mcrouper/maratui-waage/src/state/fsm.rs

use log::{error, info};

use super::global_state::MACHINE_OFFLINE_TIMEOUT;
use super::{
    AppError, AppEvent, CalibrationStep, ConnectionStatus, DeviceInfo, ExtractionState,
    GlobalAppState,
};
use crate::button::{Button, ButtonPressType};
#[cfg(feature = "home-assistant")]
use crate::home_assistant;
use crate::screens::Screen;
use crate::telemetry::{TelemetryFrame, update_state_with_events};
use std::time::{Duration, Instant};

/// Application state machine
/// Handles events and updates the global application state
pub struct AppStateMachine;

impl AppStateMachine {
    /// Handle an application event and update the state
    pub fn handle_event(state: &mut GlobalAppState, event: AppEvent) {
        info!("Handling event: {:?}", event);

        if event.is_telemetry_event() {
            state.events_log.push_front(format!("Event: {:?}", event));
            if state.events_log.len() > 10 {
                state.events_log.pop_back();
            }
        }
        match event {
            // ===== Telemetry Events =====
            AppEvent::ShotStarted => {
                state.extraction_state = ExtractionState::Extracting {
                    started_at: Instant::now(),
                };
                state.error = None;
                // Tare out whatever is currently on the scale (e.g. the empty cup) so the
                // Dashboard shows net extracted weight for this shot.
                Self::tare_scale(state);
            }

            AppEvent::ShotEnded { duration } => {
                state.extraction_state = ExtractionState::Idle {
                    last_extraction_duration: Some(Duration::from_secs(duration)),
                };
                state.last_shot_ended_at = Some(Instant::now());
            }

            AppEvent::ShotAborted { .. } => {
                state.extraction_state = ExtractionState::Idle {
                    last_extraction_duration: None,
                };
                state.last_shot_ended_at = Some(Instant::now());
            }

            AppEvent::ModeChanged { from: _, to: _ } => {
                // Machine mode is already updated in MachineState
                // Additional logic can be added here if needed
            }

            AppEvent::WaterRefillNeeded { code } => {
                state.error = Some(AppError::WaterRefillNeeded { code });
            }

            AppEvent::WaterRefillCleared => {
                state.error = None;
            }

            // ===== UI Events =====
            AppEvent::NextScreen => {
                state.current_screen = state.current_screen.next();
            }

            AppEvent::PreviousScreen => {
                state.current_screen = state.current_screen.previous();
            }

            AppEvent::DebugScreen => {
                if state.current_screen == Screen::Debug {
                    state.current_screen = state
                        .screen_before_debug
                        .take()
                        .unwrap_or(Screen::Dashboard);
                } else {
                    state.screen_before_debug = Some(state.current_screen);
                    state.current_screen = Screen::Debug;
                }
                // Debug uses a full-screen layout unrelated to the normal screens; clear so
                // nothing from the previous layout lingers.
                state.request_redraw();
            }

            AppEvent::ErrorOccurred { error } => {
                state.error = Some(AppError::MachineOffline);
                // Log the error (logging can be added here)
                error!("Application error: {}", error);
            }

            AppEvent::ErrorCleared => {
                state.error = None;
            }

            AppEvent::WifiStatusChanged(status) => {
                match &status {
                    ConnectionStatus::Connected | ConnectionStatus::Disconnected => {
                        state.events_log.push_front(format!("Wi-Fi: {:?}", status));
                        if state.events_log.len() > 10 {
                            state.events_log.pop_back();
                        }
                    }
                    _ => {}
                }
                state.wifi_status = status;
            }

            AppEvent::MqttStatusChanged(status) => {
                let should_log = match &status {
                    ConnectionStatus::Connected => state.mqtt_status != ConnectionStatus::Connected,
                    ConnectionStatus::Disconnected | ConnectionStatus::Error(_) => true,
                    _ => false,
                };
                if should_log {
                    state.events_log.push_front(format!("MQTT: {:?}", status));
                    if state.events_log.len() > 10 {
                        state.events_log.pop_back();
                    }
                }
                state.mqtt_status = status;
            }

            AppEvent::CupCounterUpdated { cups } => {
                state.cup_counter = Some(cups);
            }

            AppEvent::PublishMqttEvent {
                topic_suffix,
                payload,
            } => {
                state.enqueue_mqtt_message(topic_suffix, payload);
            }

            AppEvent::DeviceInfoUpdated(info) => {
                let payload = device_status_payload(&info);
                #[cfg(feature = "home-assistant")]
                home_assistant::enqueue_status_states(state, &info);
                state.device_info = info;
                state.enqueue_mqtt_message("status", payload);
            }

            AppEvent::LoadingStage { message, progress } => {
                state.loading_status = Some((message, progress));
            }

            AppEvent::LoadingComplete => {
                state.loading_status = Some(("waiting for machine...", 100));
            }

            AppEvent::EnterOfflineMode => {
                if state.machine_state.last_frame.is_none() {
                    state.machine_state.last_frame = Some(TelemetryFrame::offline_frame());
                    state.offline_mode = true;
                    state.last_activity_at = Some(Instant::now());
                    state.request_redraw();
                }
            }

            AppEvent::WeightUpdated { weight_dg } => {
                if state.last_raw_weight_dg.is_none() {
                    // First reading since boot: tare immediately so the Dashboard starts at
                    // 0g instead of showing whatever residual raw drift happens to be on the
                    // scale (e.g. the portafilter, or just calibration offset error).
                    state.scale_tare_dg = weight_dg;
                }
                state.last_raw_weight_dg = Some(weight_dg);
                state.weight_dg = Some(weight_dg - state.scale_tare_dg);
                Self::publish_weight_if_due(state, Instant::now());
            }

            AppEvent::RawWeightUpdated { left, right } => {
                state.raw_weight_left = left;
                state.raw_weight_right = right;
            }

            AppEvent::StartCalibration => {
                if state.calibration_step.is_none() {
                    state.screen_before_calibration = Some(state.current_screen);
                    state.calibration_step = Some(CalibrationStep::ConfirmEmptyLeft);
                    state.request_redraw();
                }
            }

            AppEvent::CalibrationConfirm => {
                state.calibration_step = match state.calibration_step {
                    Some(CalibrationStep::ConfirmEmptyLeft) => Some(CalibrationStep::TaringLeft),
                    Some(CalibrationStep::ConfirmReferenceLeft) => {
                        Some(CalibrationStep::CalibratingLeft)
                    }
                    Some(CalibrationStep::ConfirmEmptyRight) => Some(CalibrationStep::TaringRight),
                    Some(CalibrationStep::ConfirmReferenceRight) => {
                        Some(CalibrationStep::CalibratingRight)
                    }
                    // A press on the result screen dismisses the wizard.
                    Some(CalibrationStep::Done { .. }) => None,
                    other => other,
                };
                if state.calibration_step.is_none() {
                    if let Some(prev) = state.screen_before_calibration.take() {
                        state.current_screen = prev;
                    }
                    state.request_redraw();
                }
            }

            AppEvent::CalibrationCancel => {
                state.calibration_step = None;
                if let Some(prev) = state.screen_before_calibration.take() {
                    state.current_screen = prev;
                }
                state.request_redraw();
            }

            AppEvent::CalibrationStepResult { success } => {
                state.calibration_step = Some(match (state.calibration_step, success) {
                    (Some(CalibrationStep::TaringLeft), true) => {
                        CalibrationStep::ConfirmReferenceLeft
                    }
                    (Some(CalibrationStep::CalibratingLeft), true) => {
                        CalibrationStep::ConfirmEmptyRight
                    }
                    (Some(CalibrationStep::TaringRight), true) => {
                        CalibrationStep::ConfirmReferenceRight
                    }
                    (Some(CalibrationStep::CalibratingRight), true) => {
                        CalibrationStep::Done { success: true }
                    }
                    _ => CalibrationStep::Done { success: false },
                });
            }
        }
    }

    /// Handle button press events
    pub fn handle_button_press(state: &mut GlobalAppState, button: Button) {
        // While the calibration wizard is active, button presses drive it instead of the
        // usual screen navigation / Debug toggle.
        if state.calibration_step.is_some() {
            match button {
                Button::Button1(ButtonPressType::Short) => {
                    Self::handle_event(state, AppEvent::CalibrationConfirm);
                }
                Button::Button1(ButtonPressType::Long) => {
                    Self::handle_event(state, AppEvent::CalibrationCancel);
                }
                // Double press has no meaning inside the wizard; ignore it.
                Button::Button1(ButtonPressType::Double) => {}
            }
            return;
        }

        // Long press always toggles Debug, even during loading.
        if let Button::Button1(ButtonPressType::Long) = button {
            Self::handle_event(state, AppEvent::DebugScreen);
            return;
        }

        // Double press manually zeros the scale, regardless of screen — a quick way to tare
        // without waiting for a shot to start.
        if let Button::Button1(ButtonPressType::Double) = button {
            Self::tare_scale(state);
            return;
        }

        // During loading: short press manually toggles the backlight.
        if state.machine_state.last_frame.is_none() {
            if let Button::Button1(ButtonPressType::Short) = button {
                state.backlight_on = !state.backlight_on;
            }
            return;
        }

        // Normal operation after first UART frame arrives.
        let now = Instant::now();
        let backlight_was_on = state.backlight_should_be_on(now);
        state.last_activity_at = Some(now);

        // If the screen was dark (backlight timed out), the first press only wakes the
        // backlight and must not also switch screens.
        if !backlight_was_on {
            return;
        }

        if let Button::Button1(ButtonPressType::Short) = button
            && state.current_screen != Screen::Debug
        {
            Self::handle_event(state, AppEvent::NextScreen);
        }
    }

    /// Zero the scale: tare both cells against whatever they're currently reading, so the
    /// Dashboard's weight display resets to 0 g. Shared by the shot-start auto-tare and the
    /// manual double-press-to-zero gesture.
    fn tare_scale(state: &mut GlobalAppState) {
        state.scale_tare_dg = state.last_raw_weight_dg.unwrap_or(0);
        state.weight_dg = Some(0);
    }

    /// Publish the displayed (tared) weight to `<prefix>/scale` when it changed, at most once per
    /// `SCALE_PUBLISH_INTERVAL`. A change that falls inside the interval isn't lost: the scale
    /// keeps sampling, so the next `WeightUpdated` after the interval publishes the latest value.
    fn publish_weight_if_due(state: &mut GlobalAppState, now: Instant) {
        let Some(weight_dg) = state.weight_dg else {
            return;
        };
        if state.last_published_weight_dg == Some(weight_dg) {
            return;
        }
        let due = state
            .last_scale_publish_at
            .map(|t| now.saturating_duration_since(t) >= SCALE_PUBLISH_INTERVAL)
            .unwrap_or(true);
        if !due {
            return;
        }
        state.last_published_weight_dg = Some(weight_dg);
        state.last_scale_publish_at = Some(now);
        state.enqueue_mqtt_message("scale", scale_payload(weight_dg));
    }

    /// Handle telemetry frame updates
    pub fn handle_telemetry_frame(state: &mut GlobalAppState, frame: TelemetryFrame, now: Instant) {
        state.offline_mode = false;
        state.enqueue_mqtt_message("telemetry", telemetry_payload(&frame));

        // A new session starts on the very first frame, or when telemetry resumes after the
        // machine has been offline (long UART gap). Reset per-session state and ask the render
        // loop to clear the terminal so any accumulated display artifacts are wiped.
        let new_session = state
            .last_uart_frame_at
            .map(|t| now.saturating_duration_since(t) >= MACHINE_OFFLINE_TIMEOUT)
            .unwrap_or(true);
        if new_session {
            state.machine_state.reset_session();
            state.request_redraw();
        }

        // frame moves into update_state_with_events; it is stored in state.machine_state.last_frame
        let (_snapshot, events) = update_state_with_events(&mut state.machine_state, frame, now);

        // Extract Copy fields from last_frame before the mutable borrows below
        let (boiler_target, boiler_now_c, hx_now_c) = {
            let last = state
                .machine_state
                .last_frame
                .as_ref()
                .expect("update_state_with_events always stores the frame in last_frame");
            (
                last.boiler_target_c.map(f64::from).unwrap_or_default(),
                f64::from(last.boiler_now_c),
                f64::from(last.hx_now_c),
            )
        };
        let should_sample = state
            .machine_state
            .last_graph_sample_at
            .map(|t| now.saturating_duration_since(t) >= GRAPH_SAMPLE_INTERVAL)
            .unwrap_or(true);
        if should_sample {
            state.machine_state.last_graph_sample_at = Some(now);
            push_sample(&mut state.machine_state.target_boiler_data, boiler_target);
            push_sample(&mut state.machine_state.current_boiler_data, boiler_now_c);
            push_sample(&mut state.machine_state.current_hx_data, hx_now_c);
            state.machine_state.rebuild_graph_points();
        }
        state.last_activity_at = Some(now);
        state.last_uart_frame_at = Some(now);

        // Process each event through the FSM
        for event in events {
            let event_payload = telemetry_event_payload(&event, state.weight_dg);
            #[cfg(feature = "home-assistant")]
            home_assistant::enqueue_event_states(state, &event);
            Self::handle_event(state, AppEvent::from_telemetry(event));
            state.enqueue_mqtt_message("events", event_payload);
        }

        #[cfg(feature = "home-assistant")]
        home_assistant::enqueue_telemetry_states(state);
    }

    /// Handle multiple events in sequence
    pub fn handle_events(state: &mut GlobalAppState, events: Vec<AppEvent>) {
        for event in events {
            Self::handle_event(state, event);
        }
    }
}

fn json_opt_num<T: std::fmt::Display>(opt: Option<T>) -> String {
    opt.map_or_else(|| "null".to_string(), |v| v.to_string())
}

fn json_opt_str(opt: Option<&str>) -> String {
    opt.map_or_else(|| "null".to_string(), |s| format!("\"{}\"", s))
}

fn telemetry_payload(frame: &TelemetryFrame) -> String {
    format!(
        "{{\"mode\":\"{}\",\"sw\":\"{}\",\"boiler_now_c\":{},\"boiler_target_c\":{},\"hx_now_c\":{},\"boost_countdown_s\":{},\"heating_on\":{},\"pump_on\":{},\"no_water_code\":{}}}",
        frame.mode,
        frame.sw_version,
        frame.boiler_now_c,
        json_opt_num(frame.boiler_target_c),
        frame.hx_now_c,
        frame.boost_countdown_s,
        frame.heating_on,
        frame.pump_on,
        json_opt_num(frame.no_water_code),
    )
}

/// One sample per second; 300 samples = 5-minute window shown on the Graphs screen.
const GRAPH_BUF_CAP: usize = 300;
const GRAPH_SAMPLE_INTERVAL: Duration = Duration::from_secs(1);

fn push_sample(buf: &mut std::collections::VecDeque<f64>, value: f64) {
    buf.push_back(value);
    if buf.len() > GRAPH_BUF_CAP {
        buf.pop_front();
    }
}

/// Cap on `<prefix>/scale` publishes (~4 Hz), so sub-gram noise can't flood the MQTT queue.
const SCALE_PUBLISH_INTERVAL: Duration = Duration::from_millis(250);

/// Format decigrams as grams with one decimal (`-5` → `-0.5`), exact — no float rounding.
fn grams_json(weight_dg: i32) -> String {
    let sign = if weight_dg < 0 { "-" } else { "" };
    let abs = weight_dg.unsigned_abs();
    format!("{}{}.{}", sign, abs / 10, abs % 10)
}

fn opt_grams_json(weight_dg: Option<i32>) -> String {
    weight_dg.map_or_else(|| "null".to_string(), grams_json)
}

fn scale_payload(weight_dg: i32) -> String {
    format!("{{\"weight_g\":{}}}", grams_json(weight_dg))
}

fn device_status_payload(info: &DeviceInfo) -> String {
    format!(
        "{{\"uptime_s\":{},\"wifi_ssid\":\"{}\",\"wifi_rssi\":{},\"ip\":{},\"free_heap_b\":{},\"last_telemetry_age_s\":{}}}",
        info.uptime_s,
        info.wifi_ssid,
        json_opt_num(info.wifi_rssi),
        json_opt_str(info.ip.as_deref()),
        json_opt_num(info.free_heap_b),
        json_opt_num(info.last_telemetry_age_s),
    )
}

/// `weight_dg` is the net (shot-start-tared) scale weight at the moment the event fires, so for
/// `shot_ended`/`shot_aborted` it's the shot's yield; `null` without a scale.
fn telemetry_event_payload(event: &crate::telemetry::AppEvent, weight_dg: Option<i32>) -> String {
    match event {
        crate::telemetry::AppEvent::ShotStarted => "{\"type\":\"shot_started\"}".to_string(),
        crate::telemetry::AppEvent::ShotEnded { duration } => format!(
            "{{\"type\":\"shot_ended\",\"duration\":{},\"weight_g\":{}}}",
            duration,
            opt_grams_json(weight_dg)
        ),
        crate::telemetry::AppEvent::ShotAborted { duration } => format!(
            "{{\"type\":\"shot_aborted\",\"duration\":{},\"weight_g\":{}}}",
            duration,
            opt_grams_json(weight_dg)
        ),
        crate::telemetry::AppEvent::WaterRefillNeeded { code } => {
            format!("{{\"type\":\"water_refill_needed\",\"code\":{}}}", code)
        }
        crate::telemetry::AppEvent::WaterRefillCleared => {
            "{\"type\":\"water_refill_cleared\"}".to_string()
        }
        crate::telemetry::AppEvent::ModeChanged { from, to } => {
            format!(
                "{{\"type\":\"mode_changed\",\"from\":\"{}\",\"to\":\"{}\"}}",
                from, to
            )
        }
    }
}

#[cfg(test)]
mod tests {
    use super::*;
    use crate::screens::Screen;
    use crate::state::global_state::BACKLIGHT_TIMEOUT;
    use std::time::Duration;

    #[test]
    fn test_handle_shot_started() {
        let mut state = GlobalAppState::default();
        assert_eq!(
            state.extraction_state,
            ExtractionState::Idle {
                last_extraction_duration: None
            }
        );

        AppStateMachine::handle_event(&mut state, AppEvent::ShotStarted);

        assert!(state.extraction_state.is_extracting());
    }

    #[test]
    fn test_handle_shot_ended() {
        let mut state = GlobalAppState::default();
        state.extraction_state = ExtractionState::Extracting {
            started_at: Instant::now(),
        };

        let duration = Duration::from_secs(30);
        AppStateMachine::handle_event(
            &mut state,
            AppEvent::ShotEnded {
                duration: duration.as_secs(),
            },
        );

        assert_eq!(
            state.extraction_state,
            ExtractionState::Idle {
                last_extraction_duration: Some(duration)
            }
        );
    }

    #[test]
    fn test_handle_water_refill_needed() {
        let mut state = GlobalAppState::default();
        assert!(!state.has_error());

        AppStateMachine::handle_event(&mut state, AppEvent::WaterRefillNeeded { code: 65 });

        assert!(state.has_error());
        assert_eq!(state.error, Some(AppError::WaterRefillNeeded { code: 65 }));
    }

    #[test]
    fn test_handle_water_refill_cleared() {
        let mut state = GlobalAppState::default();
        state.error = Some(AppError::WaterRefillNeeded { code: 65 });

        AppStateMachine::handle_event(&mut state, AppEvent::WaterRefillCleared);

        assert!(!state.has_error());
    }

    #[test]
    fn test_handle_next_screen() {
        let mut state = GlobalAppState::default();
        let initial_screen = state.current_screen;

        AppStateMachine::handle_event(&mut state, AppEvent::NextScreen);

        assert_eq!(state.current_screen, initial_screen.next());
    }

    #[test]
    fn test_handle_previous_screen() {
        let mut state = GlobalAppState::default();
        state.current_screen = Screen::Dashboard;

        AppStateMachine::handle_event(&mut state, AppEvent::PreviousScreen);

        assert_eq!(state.current_screen, Screen::Dashboard.previous());
    }

    #[test]
    fn test_handle_button_press_short() {
        let mut state = GlobalAppState::default();
        // Navigation is blocked until first telemetry arrives
        state.machine_state.last_frame = Some(TelemetryFrame::debug_frame());
        // Backlight must be on for a press to switch screens
        state.last_activity_at = Some(Instant::now());
        let initial_screen = state.current_screen;

        AppStateMachine::handle_button_press(&mut state, Button::Button1(ButtonPressType::Short));

        assert_eq!(state.current_screen, initial_screen.next());
    }

    #[test]
    fn test_press_while_dark_only_wakes_backlight() {
        let mut state = GlobalAppState::default();
        state.machine_state.last_frame = Some(TelemetryFrame::debug_frame());
        // Backlight timed out (last activity well in the past)
        state.last_activity_at = Some(Instant::now() - BACKLIGHT_TIMEOUT - Duration::from_secs(1));
        let initial_screen = state.current_screen;

        AppStateMachine::handle_button_press(&mut state, Button::Button1(ButtonPressType::Short));

        // First press only wakes the backlight: screen must not change, activity refreshed
        assert_eq!(state.current_screen, initial_screen);
        assert!(state.backlight_should_be_on(Instant::now()));

        // Second press (backlight now on) switches screens
        AppStateMachine::handle_button_press(&mut state, Button::Button1(ButtonPressType::Short));
        assert_eq!(state.current_screen, initial_screen.next());
    }

    fn scale_messages(state: &mut GlobalAppState) -> Vec<String> {
        state
            .take_outbound_mqtt_messages()
            .into_iter()
            .filter(|m| m.topic_suffix == "scale")
            .map(|m| m.payload)
            .collect()
    }

    #[test]
    fn test_weight_published_on_change_and_rate_limited() {
        let mut state = GlobalAppState::default();
        let t0 = Instant::now();
        state.weight_dg = Some(0);
        AppStateMachine::publish_weight_if_due(&mut state, t0);
        assert_eq!(scale_messages(&mut state), vec![r#"{"weight_g":0.0}"#]);

        // Unchanged weight: nothing sent, even long after the interval
        AppStateMachine::publish_weight_if_due(&mut state, t0 + Duration::from_secs(5));
        assert!(scale_messages(&mut state).is_empty());

        // Changed within the interval: held back...
        let t1 = t0 + Duration::from_secs(10);
        state.weight_dg = Some(123);
        AppStateMachine::publish_weight_if_due(&mut state, t1);
        state.weight_dg = Some(187);
        AppStateMachine::publish_weight_if_due(&mut state, t1 + Duration::from_millis(100));
        assert_eq!(scale_messages(&mut state), vec![r#"{"weight_g":12.3}"#]);

        // ...and the latest value goes out on the next sample after the interval
        AppStateMachine::publish_weight_if_due(&mut state, t1 + SCALE_PUBLISH_INTERVAL);
        assert_eq!(scale_messages(&mut state), vec![r#"{"weight_g":18.7}"#]);
    }

    #[test]
    fn test_weight_updated_publishes_scale_topic() {
        let mut state = GlobalAppState::default();
        AppStateMachine::handle_event(&mut state, AppEvent::WeightUpdated { weight_dg: 100 });
        assert_eq!(scale_messages(&mut state), vec![r#"{"weight_g":0.0}"#]);
    }

    #[test]
    fn test_grams_json_formats_decigrams_exactly() {
        assert_eq!(grams_json(0), "0.0");
        assert_eq!(grams_json(362), "36.2");
        assert_eq!(grams_json(-5), "-0.5");
        assert_eq!(grams_json(-123), "-12.3");
    }

    #[test]
    fn test_shot_events_carry_weight() {
        use crate::telemetry::AppEvent as TelemetryEvent;
        assert_eq!(
            telemetry_event_payload(&TelemetryEvent::ShotEnded { duration: 28 }, Some(362)),
            r#"{"type":"shot_ended","duration":28,"weight_g":36.2}"#
        );
        assert_eq!(
            telemetry_event_payload(&TelemetryEvent::ShotAborted { duration: 4 }, None),
            r#"{"type":"shot_aborted","duration":4,"weight_g":null}"#
        );
    }

    #[test]
    fn test_double_press_zeroes_the_scale() {
        let mut state = GlobalAppState::default();
        state.machine_state.last_frame = Some(TelemetryFrame::debug_frame());
        state.last_activity_at = Some(Instant::now());
        // First reading since boot is auto-tared to zero; load the scale afterwards so there's
        // something non-zero on screen for the double press to zero back out.
        AppStateMachine::handle_event(&mut state, AppEvent::WeightUpdated { weight_dg: 100 });
        AppStateMachine::handle_event(&mut state, AppEvent::WeightUpdated { weight_dg: 1334 });
        assert_eq!(state.weight_dg, Some(1234));

        AppStateMachine::handle_button_press(&mut state, Button::Button1(ButtonPressType::Double));

        assert_eq!(state.scale_tare_dg, 1334);
        assert_eq!(state.weight_dg, Some(0));
    }

    #[test]
    fn test_double_press_zeroes_the_scale_even_before_telemetry_or_backlight_wake() {
        let mut state = GlobalAppState::default();
        // No telemetry yet, and the backlight has timed out — both would block a Short press,
        // but zeroing the scale is a physical action that should always work.
        assert!(state.machine_state.last_frame.is_none());
        state.last_activity_at = Some(Instant::now() - BACKLIGHT_TIMEOUT - Duration::from_secs(1));
        AppStateMachine::handle_event(&mut state, AppEvent::WeightUpdated { weight_dg: 100 });
        AppStateMachine::handle_event(&mut state, AppEvent::WeightUpdated { weight_dg: 600 });
        assert_eq!(state.weight_dg, Some(500));

        AppStateMachine::handle_button_press(&mut state, Button::Button1(ButtonPressType::Double));

        assert_eq!(state.scale_tare_dg, 600);
        assert_eq!(state.weight_dg, Some(0));
    }

    #[test]
    fn test_double_press_is_ignored_during_calibration_wizard() {
        let mut state = GlobalAppState::default();
        state.machine_state.last_frame = Some(TelemetryFrame::debug_frame());
        AppStateMachine::handle_event(&mut state, AppEvent::WeightUpdated { weight_dg: 999 });
        AppStateMachine::handle_event(&mut state, AppEvent::StartCalibration);
        let tare_before = state.scale_tare_dg;

        AppStateMachine::handle_button_press(&mut state, Button::Button1(ButtonPressType::Double));

        // Unchanged: a double press must not interfere with the wizard's own confirm/cancel flow.
        assert_eq!(state.scale_tare_dg, tare_before);
    }

    #[test]
    fn test_telemetry_resume_starts_new_session() {
        let mut state = GlobalAppState::default();
        let t0 = Instant::now();

        // First frame: a shot runs and is sampled into the graph buffers.
        let on = TelemetryFrame::debug_pump_on_frame();
        AppStateMachine::handle_telemetry_frame(&mut state, on, t0);
        assert!(state.take_redraw_request(), "first frame starts a session");
        assert!(!state.machine_state.current_boiler_data.is_empty());

        // Telemetry resumes after the machine was offline: buffers reset, redraw requested,
        // and no spurious shot-end event is logged from the stale pump-on frame.
        let events_before = state.events_log.len();
        let resume = TelemetryFrame::debug_frame();
        AppStateMachine::handle_telemetry_frame(
            &mut state,
            resume,
            t0 + MACHINE_OFFLINE_TIMEOUT + Duration::from_secs(1),
        );
        assert!(state.take_redraw_request(), "resume starts a new session");
        // Exactly one fresh sample after the reset (no stale history)
        assert_eq!(state.machine_state.current_boiler_data.len(), 1);
        assert_eq!(
            state.events_log.len(),
            events_before,
            "no phantom transition events on resume"
        );
    }

    #[test]
    fn test_handle_button_press_blocked_before_telemetry() {
        let mut state = GlobalAppState::default();
        assert!(state.machine_state.last_frame.is_none());
        let initial_screen = state.current_screen;

        AppStateMachine::handle_button_press(&mut state, Button::Button1(ButtonPressType::Short));

        // Screen must not change while no telemetry
        assert_eq!(state.current_screen, initial_screen);
    }

    #[test]
    fn test_loading_short_press_toggles_backlight() {
        let mut state = GlobalAppState::default();
        assert!(state.machine_state.last_frame.is_none());
        assert!(state.backlight_on);

        AppStateMachine::handle_button_press(&mut state, Button::Button1(ButtonPressType::Short));
        assert!(!state.backlight_on);

        AppStateMachine::handle_button_press(&mut state, Button::Button1(ButtonPressType::Short));
        assert!(state.backlight_on);
    }

    #[test]
    fn test_handle_multiple_events() {
        let mut state = GlobalAppState::default();

        let events = vec![
            AppEvent::ShotStarted,
            AppEvent::NextScreen,
            AppEvent::WaterRefillNeeded { code: 65 },
        ];

        AppStateMachine::handle_events(&mut state, events);

        assert!(state.extraction_state.is_extracting());
        assert!(state.has_error());
    }

    #[test]
    fn test_shot_started_clears_error() {
        let mut state = GlobalAppState::default();
        state.error = Some(AppError::WaterRefillNeeded { code: 65 });

        AppStateMachine::handle_event(&mut state, AppEvent::ShotStarted);

        assert!(!state.has_error());
    }

    #[test]
    fn test_first_weight_reading_since_boot_is_tared_to_zero() {
        let mut state = GlobalAppState::default();

        // Whatever is on the scale at boot (residual raw drift, an empty portafilter, ...)
        // becomes the zero point immediately, rather than showing as a nonzero weight until
        // the first shot starts.
        AppStateMachine::handle_event(&mut state, AppEvent::WeightUpdated { weight_dg: 1234 });

        assert_eq!(state.weight_dg, Some(0));
        assert_eq!(state.scale_tare_dg, 1234);
    }

    #[test]
    fn test_subsequent_weight_readings_use_the_boot_tare() {
        let mut state = GlobalAppState::default();

        AppStateMachine::handle_event(&mut state, AppEvent::WeightUpdated { weight_dg: 1000 });
        AppStateMachine::handle_event(&mut state, AppEvent::WeightUpdated { weight_dg: 1500 });

        // Tare stays at the first reading; later readings are net of it.
        assert_eq!(state.weight_dg, Some(500));
        assert_eq!(state.scale_tare_dg, 1000);
    }

    #[test]
    fn test_shot_started_retares_on_top_of_the_boot_tare() {
        let mut state = GlobalAppState::default();

        // Boot tare from residual drift.
        AppStateMachine::handle_event(&mut state, AppEvent::WeightUpdated { weight_dg: 1000 });
        // Cup placed on the scale before the shot starts.
        AppStateMachine::handle_event(&mut state, AppEvent::WeightUpdated { weight_dg: 1300 });
        assert_eq!(state.weight_dg, Some(300));

        AppStateMachine::handle_event(&mut state, AppEvent::ShotStarted);
        assert_eq!(state.weight_dg, Some(0));
        assert_eq!(state.scale_tare_dg, 1300);
    }

    #[test]
    fn test_extraction_duration_persistence() {
        let mut state = GlobalAppState::default();

        // Start extraction
        AppStateMachine::handle_event(&mut state, AppEvent::ShotStarted);
        assert!(state.extraction_state.is_extracting());
        assert_eq!(state.extraction_state.last_extraction_duration(), None);

        // End extraction with 30 second duration
        let duration = Duration::from_secs(30);
        AppStateMachine::handle_event(
            &mut state,
            AppEvent::ShotEnded {
                duration: duration.as_secs(),
            },
        );

        // Verify duration is stored
        assert!(!state.extraction_state.is_extracting());
        assert_eq!(
            state.extraction_state.last_extraction_duration(),
            Some(duration)
        );

        // Start new extraction
        AppStateMachine::handle_event(&mut state, AppEvent::ShotStarted);
        assert!(state.extraction_state.is_extracting());
        // Previous duration should be cleared when new extraction starts
        assert_eq!(state.extraction_state.last_extraction_duration(), None);
    }

    #[test]
    fn test_handle_cup_counter_updated() {
        let mut state = GlobalAppState::default();
        assert_eq!(state.cup_counter, None);

        AppStateMachine::handle_event(&mut state, AppEvent::CupCounterUpdated { cups: 42 });

        assert_eq!(state.cup_counter, Some(42));
    }

    #[test]
    fn test_shot_aborted_resets_timer() {
        let mut state = GlobalAppState::default();

        // Simulate a previous real shot
        AppStateMachine::handle_event(&mut state, AppEvent::ShotStarted);
        AppStateMachine::handle_event(&mut state, AppEvent::ShotEnded { duration: 30 });
        assert!(state.extraction_state.last_extraction_duration().is_some());

        // Short pump run — must not overwrite last_extraction_duration
        AppStateMachine::handle_event(&mut state, AppEvent::ShotStarted);
        AppStateMachine::handle_event(&mut state, AppEvent::ShotAborted { duration: 8 });

        assert!(!state.extraction_state.is_extracting());
        assert_eq!(state.extraction_state.last_extraction_duration(), None);
    }

    #[test]
    fn test_debug_screen_toggle() {
        let mut state = GlobalAppState::default();
        state.current_screen = Screen::Dashboard;

        // Enter Debug
        AppStateMachine::handle_event(&mut state, AppEvent::DebugScreen);
        assert_eq!(state.current_screen, Screen::Debug);

        // Toggle back — should return to Dashboard
        AppStateMachine::handle_event(&mut state, AppEvent::DebugScreen);
        assert_eq!(state.current_screen, Screen::Dashboard);
        assert!(state.screen_before_debug.is_none());
    }

    #[test]
    fn test_debug_screen_toggle_fallback_to_dashboard() {
        let mut state = GlobalAppState::default();
        // Enter Debug without prior screen set (default Dashboard)
        AppStateMachine::handle_event(&mut state, AppEvent::DebugScreen);
        AppStateMachine::handle_event(&mut state, AppEvent::DebugScreen);
        assert_eq!(state.current_screen, Screen::Dashboard);
    }

    #[test]
    fn test_calibration_start_saves_screen_and_sets_confirm_left_empty() {
        let mut state = GlobalAppState::default();
        state.current_screen = Screen::Graphs;

        AppStateMachine::handle_event(&mut state, AppEvent::StartCalibration);

        assert_eq!(state.calibration_step, Some(CalibrationStep::ConfirmEmptyLeft));
        assert_eq!(state.screen_before_calibration, Some(Screen::Graphs));
    }

    #[test]
    fn test_calibration_confirm_advances_left_then_right_steps() {
        let mut state = GlobalAppState::default();
        state.calibration_step = Some(CalibrationStep::ConfirmEmptyLeft);
        AppStateMachine::handle_event(&mut state, AppEvent::CalibrationConfirm);
        assert_eq!(state.calibration_step, Some(CalibrationStep::TaringLeft));

        state.calibration_step = Some(CalibrationStep::ConfirmReferenceLeft);
        AppStateMachine::handle_event(&mut state, AppEvent::CalibrationConfirm);
        assert_eq!(state.calibration_step, Some(CalibrationStep::CalibratingLeft));

        state.calibration_step = Some(CalibrationStep::ConfirmEmptyRight);
        AppStateMachine::handle_event(&mut state, AppEvent::CalibrationConfirm);
        assert_eq!(state.calibration_step, Some(CalibrationStep::TaringRight));
    }

    #[test]
    fn test_calibration_step_result_transitions_for_both_cells() {
        let mut state = GlobalAppState::default();

        state.calibration_step = Some(CalibrationStep::TaringLeft);
        AppStateMachine::handle_event(&mut state, AppEvent::CalibrationStepResult { success: true });
        assert_eq!(state.calibration_step, Some(CalibrationStep::ConfirmReferenceLeft));

        state.calibration_step = Some(CalibrationStep::CalibratingLeft);
        AppStateMachine::handle_event(&mut state, AppEvent::CalibrationStepResult { success: true });
        assert_eq!(state.calibration_step, Some(CalibrationStep::ConfirmEmptyRight));

        state.calibration_step = Some(CalibrationStep::TaringRight);
        AppStateMachine::handle_event(&mut state, AppEvent::CalibrationStepResult { success: true });
        assert_eq!(state.calibration_step, Some(CalibrationStep::ConfirmReferenceRight));

        state.calibration_step = Some(CalibrationStep::CalibratingRight);
        AppStateMachine::handle_event(&mut state, AppEvent::CalibrationStepResult { success: true });
        assert_eq!(state.calibration_step, Some(CalibrationStep::Done { success: true }));

        state.calibration_step = Some(CalibrationStep::TaringLeft);
        AppStateMachine::handle_event(&mut state, AppEvent::CalibrationStepResult { success: false });
        assert_eq!(state.calibration_step, Some(CalibrationStep::Done { success: false }));
    }

    #[test]
    fn test_calibration_cancel_restores_previous_screen() {
        let mut state = GlobalAppState::default();
        state.current_screen = Screen::Debug;
        state.screen_before_calibration = Some(Screen::Graphs);
        state.calibration_step = Some(CalibrationStep::ConfirmReferenceRight);

        AppStateMachine::handle_event(&mut state, AppEvent::CalibrationCancel);

        assert_eq!(state.calibration_step, None);
        assert_eq!(state.current_screen, Screen::Graphs);
    }

    #[test]
    fn test_calibration_confirm_on_done_dismisses_wizard() {
        let mut state = GlobalAppState::default();
        state.current_screen = Screen::Dashboard;
        state.screen_before_calibration = Some(Screen::Dashboard);
        state.calibration_step = Some(CalibrationStep::Done { success: true });

        AppStateMachine::handle_event(&mut state, AppEvent::CalibrationConfirm);

        assert_eq!(state.calibration_step, None);
    }

    #[test]
    fn test_button_press_during_calibration_confirms_and_cancels() {
        let mut state = GlobalAppState::default();
        state.calibration_step = Some(CalibrationStep::ConfirmEmptyLeft);

        AppStateMachine::handle_button_press(&mut state, Button::Button1(ButtonPressType::Short));
        assert_eq!(state.calibration_step, Some(CalibrationStep::TaringLeft));

        AppStateMachine::handle_button_press(&mut state, Button::Button1(ButtonPressType::Long));
        assert_eq!(state.calibration_step, None);
    }
}
