mcrouper/maratui-waage/src/state/mod.rs

pub mod app_events;
pub mod fsm;
pub mod global_state;

pub use app_events::AppEvent;
pub use fsm::AppStateMachine;
pub use global_state::{
    AppError, CalibrationStep, ConnectionStatus, DeviceInfo, ExtractionState, GlobalAppState,
    MqttOutboundMessage,
};
